Ahmed-Elnafadi/ATMEGA-Board/Flyer/ATmega 32-1.png

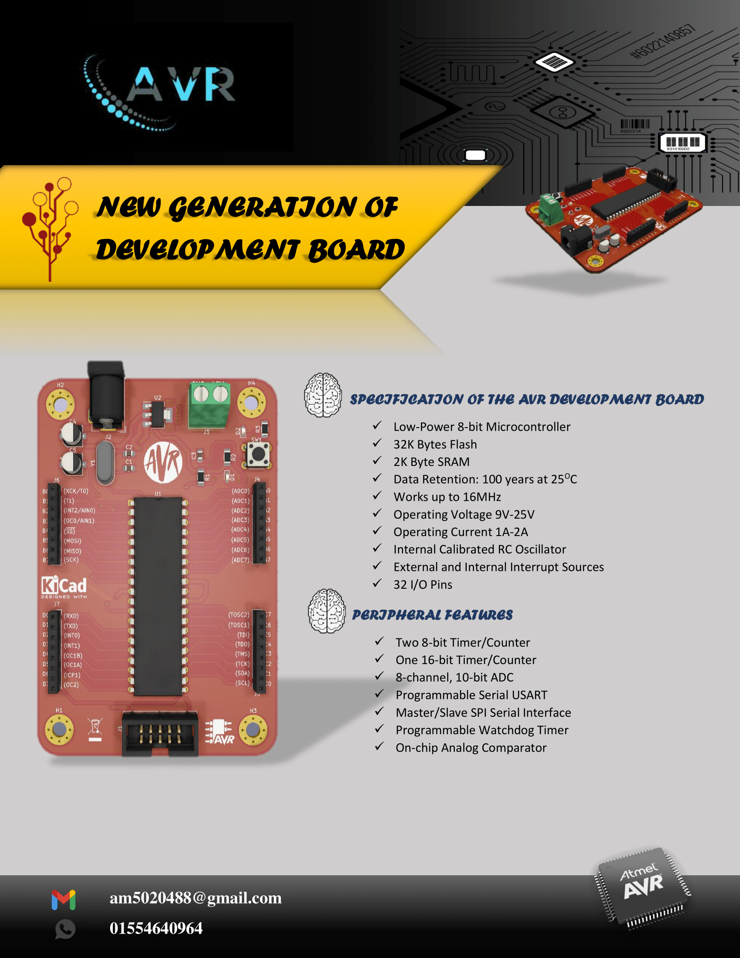
Flyer/ATmega 32-1.png
